uzi18/sterownik/arduino/dokumentacja/pics/Detektor-0.png

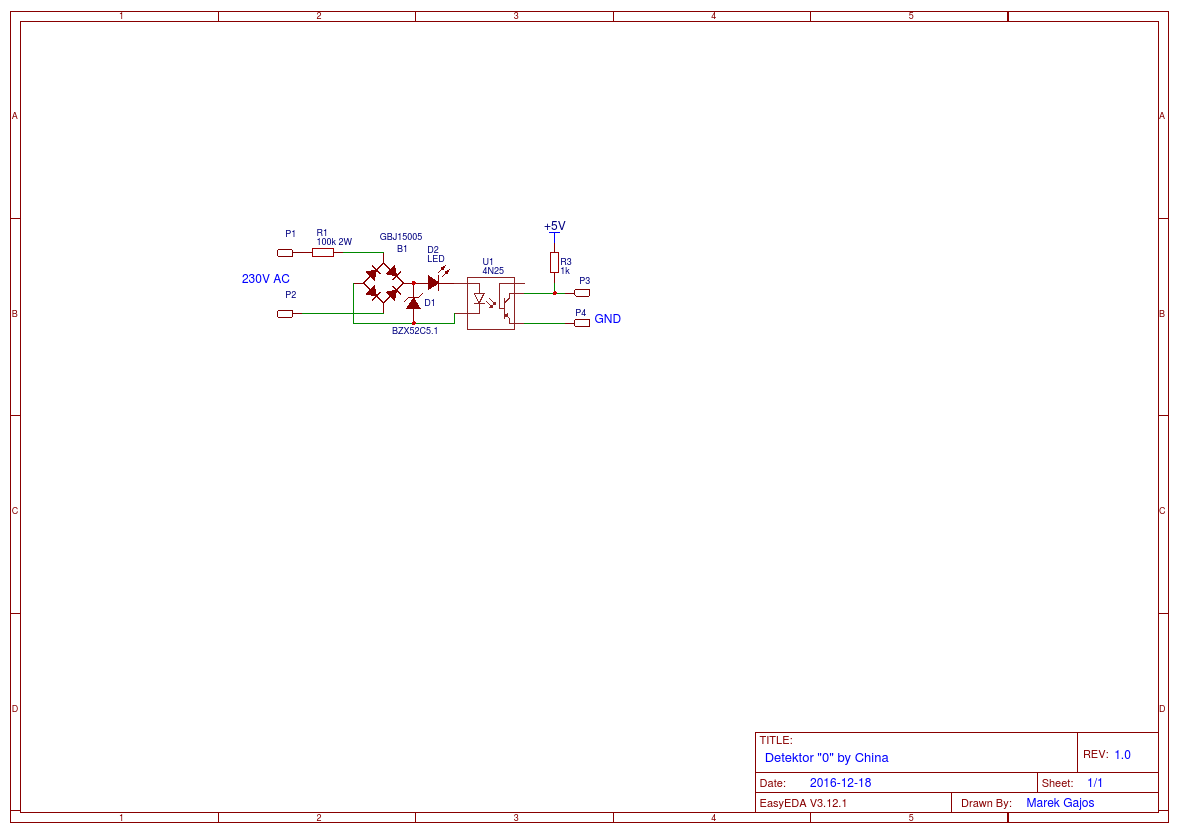
arduino/dokumentacja/pics/Detektor-0.png
