uzi18/sterownik/arduino/img/pierwsze_uruchomienie/config.jpg

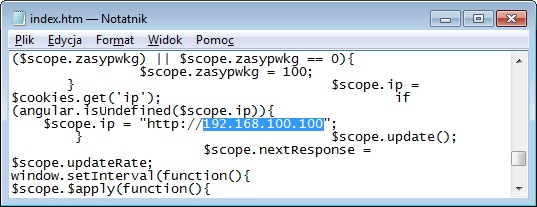
arduino/img/pierwsze_uruchomienie/config.jpg
