uzi18/sterownik/arduino/img/pierwsze_uruchomienie/eth.jpg

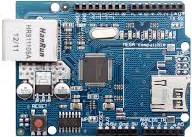
arduino/img/pierwsze_uruchomienie/eth.jpg
