uzi18/sterownik/arduino/img/pierwsze_uruchomienie/github.jpg

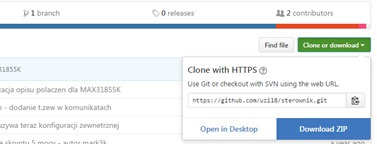
arduino/img/pierwsze_uruchomienie/github.jpg
