uzi18/sterownik/arduino/img/pierwsze_uruchomienie/mega.jpg

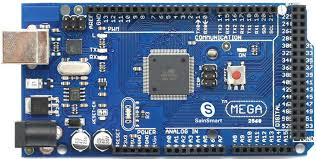
arduino/img/pierwsze_uruchomienie/mega.jpg
