uzi18/sterownik/arduino/img/pierwsze_uruchomienie/putty.jpg

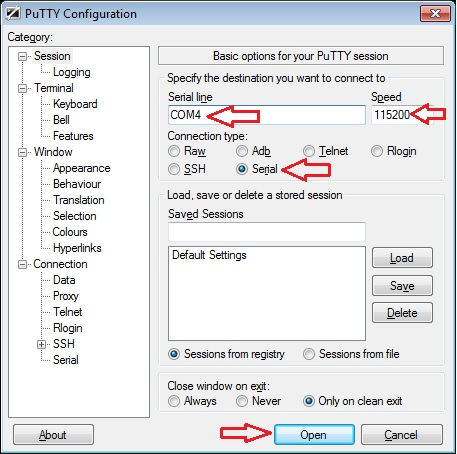
arduino/img/pierwsze_uruchomienie/putty.jpg
