uzi18/sterownik/arduino/img/pierwsze_uruchomienie/sd1.jpg

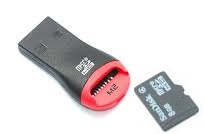
arduino/img/pierwsze_uruchomienie/sd1.jpg
