uzi18/sterownik/arduino/img/pierwsze_uruchomienie/usb.jpg

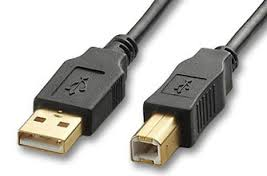
arduino/img/pierwsze_uruchomienie/usb.jpg
