uzi18/sterownik/arduino/img/pierwsze_uruchomienie/Xloader.jpg

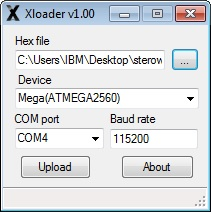
arduino/img/pierwsze_uruchomienie/Xloader.jpg
