uzi18/sterownik/podprojekty/plytki/triaki/triaki _2 schemat.png

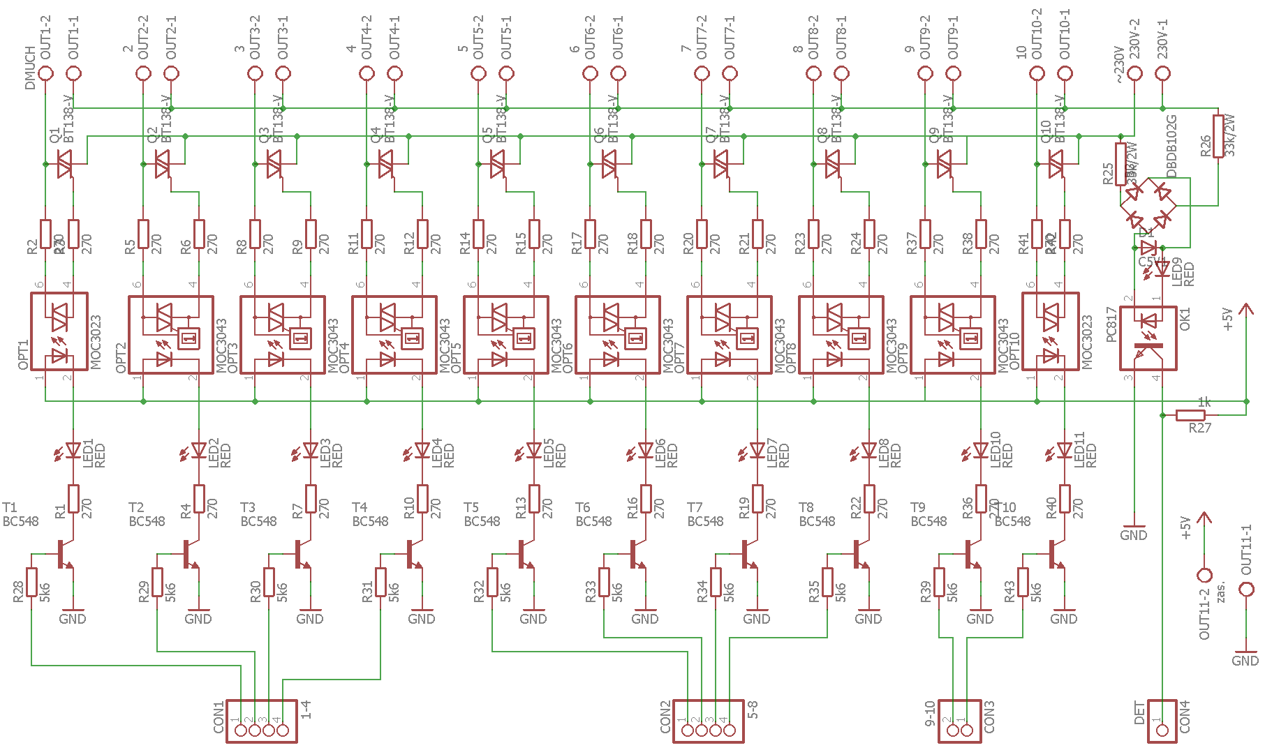
podprojekty/plytki/triaki/triaki _2 schemat.png
