uzi18/sterownik/podprojekty/plytki/triaki/triaki schemat.png

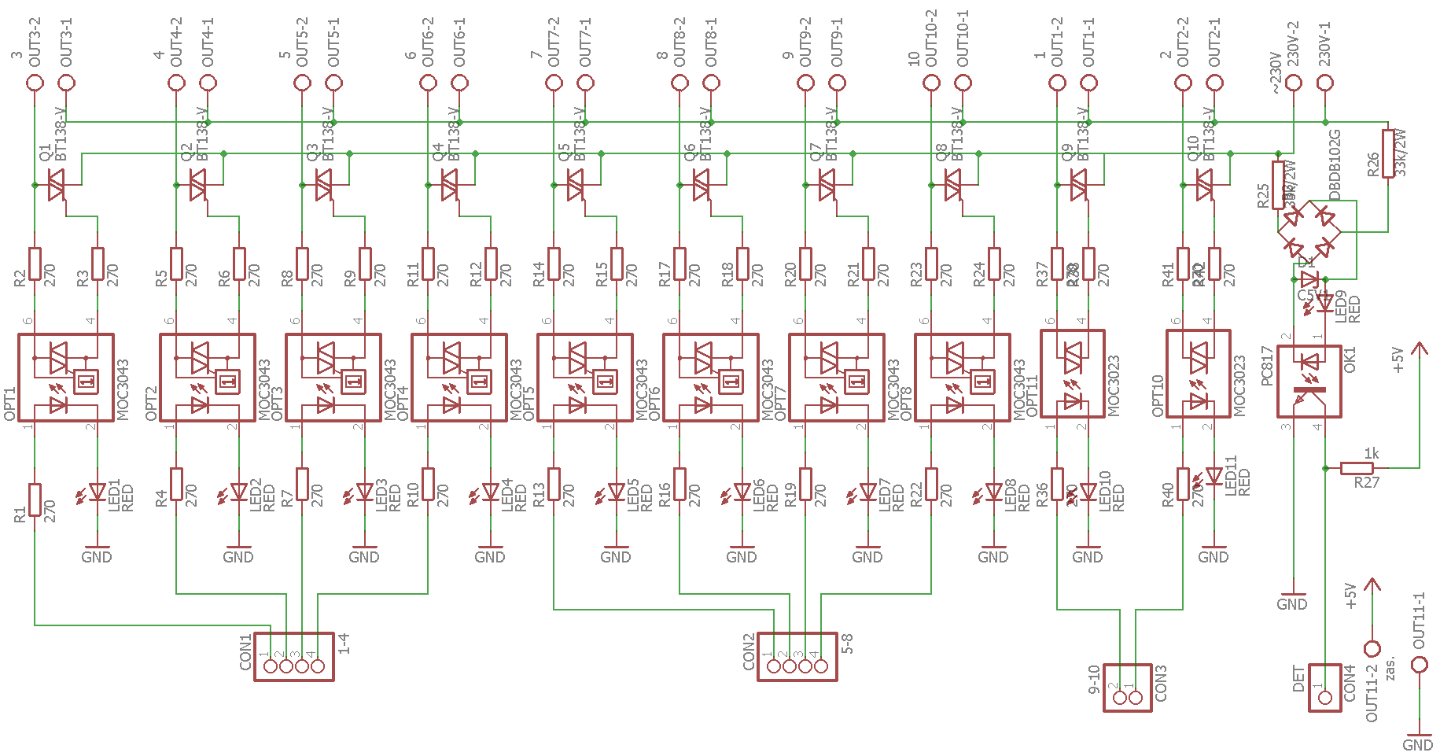
podprojekty/plytki/triaki/triaki schemat.png
