uzi18/sterownik/podprojekty/plytki/triaki/triaki samodzielne mniejsze_ver.4.pdf

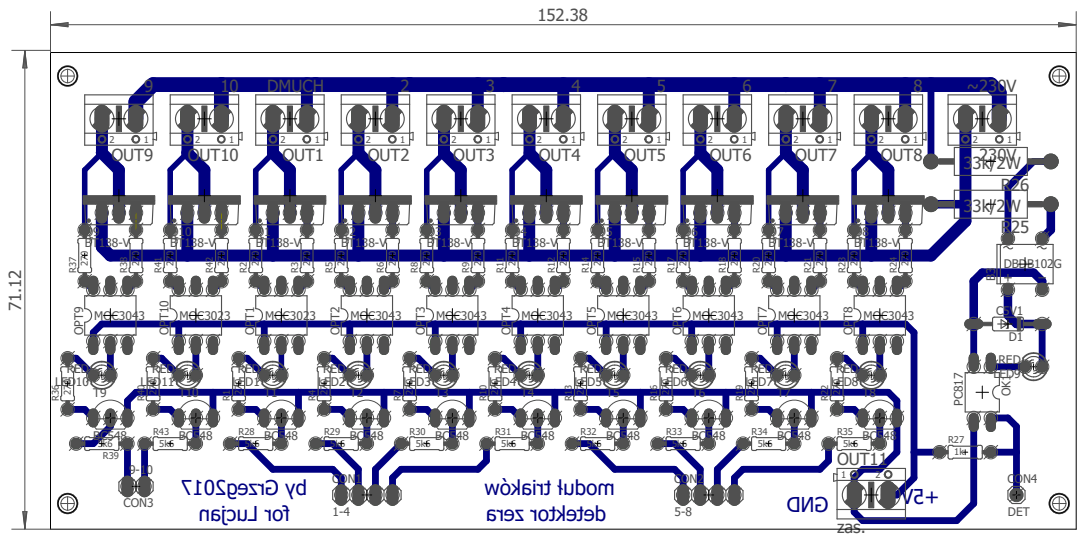
[picture p30: page 1]
