uzi18/sterownik/arduino/Domoticz/konfiguracja.py

# polaczenie z ethernet shield:
ip_lucjan = '192.168.2.4'
# lub polaczenie przez port szeregory:
#ip_lucjan = '/dev/ttyACM0'
ip_esp = '192.168.2.6'
# 1 - polaczenie przez esp_link:
esp_link = 0
# uwaga Domoticz nie akceptuje polaczenia localhost, nalezy pisac 127.0.0.1
#ip_domoticz = '127.0.0.1'
port_domoticz = 8080
idx_start = 1
ip_nettemp = 'localhost'
key_nettemp = 'xxxx'
interwal = 30
interwal_nettemp = 5
interwal_domoticz = 30

idx_zasobnik_cm = 0
idx_zasobnik_procent = 0
